Bemeier/bmcv/tests/test_instance.c

// One module per BmcvInstance, with nothing shared behind its back.
//
// The firmware only ever has one module, so a global clock and a file-static
// error latch were harmless there. A simulator or a VCV Rack patch can hold
// several, and two of them sharing a tempo is the kind of bug that is very
// hard to see and impossible to work around. These tests are what keep that
// state out of file scope.

#include "clock_sync.h"
#include "error.h"
#include "hw_setup.h"
#include "instance.h"
#include "presets.h"
#include "testkit.h"
#include "ui_input.h"
#include <string.h>

// A preset backend per instance, so "stored config" is not shared either.
typedef struct
{
  EngineConfig slots[FRAM_CONFIG_SLOTS];
  uint8_t occupied[FRAM_CONFIG_SLOTS];
  int stores;
  int loads;
  int clears;
} FakeFram;

static int8_t fake_store(void* user, const EngineConfig* cfg, int8_t slot)
{
  FakeFram* f = (FakeFram*) user;
  if (slot < 0 || slot >= FRAM_CONFIG_SLOTS)
    return 0;
  f->slots[slot]    = *cfg;
  f->occupied[slot] = 1;
  f->stores++;
  return 1;
}

static int8_t fake_clear(void* user)
{
  FakeFram* f = (FakeFram*) user;
  memset(f->occupied, 0, sizeof(f->occupied));
  f->clears++;
  return 1;
}

static int8_t fake_load(void* user, EngineConfig* cfg, int8_t slot)
{
  FakeFram* f = (FakeFram*) user;
  if (slot < 0 || slot >= FRAM_CONFIG_SLOTS || !f->occupied[slot])
    return 0;
  *cfg = f->slots[slot];
  f->loads++;
  return 1;
}

static void tick(BmcvInstance* m, const InputSample* s, uint32_t now_us) { bmcv_instance_tick(m, s, now_us); }

TEST_CASE(a_fresh_instance_comes_up_with_first_boot_defaults)
{
  BmcvInstance m;
  bmcv_instance_init(&m, NULL, 0);

  // No PresetIo means nothing was stored, which is the first-boot path.
  CHECK(m.engine_config.input_mode[0] == INPUT_CLOCK);
  CHECK(m.engine_config.input_mode[1] == INPUT_RESET);
  CHECK(m.engine_config.scene_a == 0);
  CHECK(m.engine_config.scene_b == 6);
  CHECK(m.engine_config.quantize_mask == 0b111111111111);

  // A module that has never been used is not in an error state: no stored
  // config is the expected condition, and config_validate has already made the
  // defaults safe to index.
  CHECK(!error_any(&m.engine_state));

  // And the UxState is fully wired, so a tick is safe immediately.
  CHECK(m.ux.hw_setup == m.hw_setup);
  CHECK(m.ux.ux_setup == m.ux_setup);
  CHECK(m.ux.engine_config == &m.engine_config);
  CHECK(m.ux.engine_state == &m.engine_state);
  CHECK(m.ux.ui == &m.ui_state);
  CHECK(m.ux.hw_state != NULL);
  CHECK(m.ui_state.momentary_scene == -1);

  InputSample s;
  memset(&s, 0, sizeof(s));
  s.slider_raw = SLIDER_MIN_VALUE;
  tick(&m, &s, MS(1));
}

TEST_CASE(a_stored_config_is_loaded_instead_of_the_defaults)
{
  FakeFram fram;
  memset(&fram, 0, sizeof(fram));

  EngineConfig saved;
  memset(&saved, 0, sizeof(saved));
  saved.scene_a       = 2;
  saved.scene_b       = 3;
  saved.quantize_mask = 0b101010101010;
  for (uint8_t c = 0; c < N_ENCODERS; c++)
  {
    saved.channel_state[c].src_input = -1;
    saved.channel_state[c].src_trig  = -1;
  }
  fram.slots[FRAM_CONFIG_SLOTS - 1]    = saved;
  fram.occupied[FRAM_CONFIG_SLOTS - 1] = 1;

  PresetIo io = {.store = fake_store, .load = fake_load, .user = &fram};

  BmcvInstance m;
  bmcv_instance_init(&m, &io, 0);

  CHECK(fram.loads == 1);
  CHECK(m.engine_config.scene_a == 2);
  CHECK(m.engine_config.scene_b == 3);
  CHECK(!error_any(&m.engine_state)); // nothing went wrong, so no error shown
}

// A module comes back on the parameter page it was left on. This is what the
// field moved out of UiState for: UiState is the half that is deliberately not
// saved, so while it lived there every power cycle landed on a fixed page.
TEST_CASE(the_selected_parameter_survives_a_power_cycle)
{
  FakeFram fram;
  memset(&fram, 0, sizeof(fram));
  PresetIo io = {.store = fake_store, .load = fake_load, .user = &fram};

  BmcvInstance m;
  bmcv_instance_init(&m, &io, 0);
  CHECK(m.engine_config.selected_param == CH_PARAM_OFS); // nothing stored yet

  // The user picks a page, and the autosave slot takes it.
  m.engine_config.selected_param = CH_PARAM_PHS;
  CHECK(ux_preset_store(&m.ux, CONFIG_AUTOSAVE_SLOT) == 1);

  // Power cycle: a brand new instance over the same storage.
  BmcvInstance again;
  bmcv_instance_init(&again, &io, 0);
  CHECK(again.engine_config.selected_param == CH_PARAM_PHS);
}

// ...and with nothing stored at all it is OFS, not whatever a zeroed byte
// would have made it.
TEST_CASE(a_first_boot_selects_the_offset_parameter)
{
  BmcvInstance m;
  bmcv_instance_init(&m, NULL, 0);
  CHECK(m.engine_config.selected_param == CH_PARAM_OFS);
}

// The point of the whole exercise.
TEST_CASE(two_instances_run_independent_clocks)
{
  BmcvInstance a, b;
  bmcv_instance_init(&a, NULL, 0);
  bmcv_instance_init(&b, NULL, 0);

  InputSample sa, sb;
  memset(&sa, 0, sizeof(sa));
  memset(&sb, 0, sizeof(sb));
  sa.slider_raw = SLIDER_MIN_VALUE;
  sb.slider_raw = SLIDER_MIN_VALUE;

  // Both boot with input 0 as INPUT_CLOCK. Feed a at 2Hz and b at 1Hz.
  uint8_t clock_ch = a.hw_setup->input_adc_idx[0];

  uint32_t t = 0;
  for (int i = 0; i < 40; i++)
  {
    t += MS(125);

    sa.cv_trig[clock_ch] = 1;
    tick(&a, &sa, t);
    sa.cv_trig[clock_ch] = 0;

    if (i % 2 == 1) // half as often
    {
      sb.cv_trig[clock_ch] = 1;
      tick(&b, &sb, t);
      sb.cv_trig[clock_ch] = 0;
    }
    else
    {
      tick(&b, &sb, t);
    }
  }

  CHECK_NEAR(a.engine_state.clock.beat_freq_smooth, 2.0, 0.05);
  CHECK_NEAR(b.engine_state.clock.beat_freq_smooth, 1.0, 0.05);
  CHECK(a.engine_state.clock.beat_counter != b.engine_state.clock.beat_counter);
}

TEST_CASE(two_instances_do_not_share_error_flags)
{
  BmcvInstance a, b;
  bmcv_instance_init(&a, NULL, 0);
  bmcv_instance_init(&b, NULL, 0);

  CHECK(!error_any(&a.engine_state));
  CHECK(!error_any(&b.engine_state));

  error_set(&a.engine_state, 3);
  CHECK(error_get(&a.engine_state, 3));
  CHECK(!error_get(&b.engine_state, 3));
  CHECK(!error_any(&b.engine_state));

  error_clear(&a.engine_state);
  error_set(&b.engine_state, 5);
  CHECK(!error_any(&a.engine_state));
  CHECK(error_get(&b.engine_state, 5));
}

TEST_CASE(two_instances_do_not_share_input_or_ui_state)
{
  BmcvInstance a, b;
  bmcv_instance_init(&a, NULL, 0);
  bmcv_instance_init(&b, NULL, 0);

  InputSample sa, sb;
  memset(&sa, 0, sizeof(sa));
  memset(&sb, 0, sizeof(sb));
  sa.slider_raw = 4000;
  sb.slider_raw = 6000;

  int8_t btn          = a.ux_setup->ctrl_buttons[SHIFT_STATE_QNT].button;
  sa.button_down[btn] = 1;
  sa.encoder_pos[0]   = 17;

  // Long enough for the QNT hold to cross UI_T_HOLD and latch the mode.
  // Against the constant, not a number that happened to clear it once.
  for (uint32_t i = 1; i <= UI_T_HOLD / MS(1) + 50; i++)
  {
    tick(&a, &sa, MS(i));
    tick(&b, &sb, MS(i));
  }

  CHECK(a.ux.hw_state->slider_state == 4000);
  CHECK(b.ux.hw_state->slider_state == 6000);
  CHECK(a.ux.hw_state->button_state[btn] == 1);
  CHECK(b.ux.hw_state->button_state[btn] == 0);
  CHECK(a.ux.hw_state->encoder_state[0] == 17);
  CHECK(b.ux.hw_state->encoder_state[0] == 0);

  // Holding QNT put a into that mode; b must be untouched.
  CHECK(a.ui_state.shift_state == SHIFT_STATE_QNT);
  CHECK(b.ui_state.shift_state == SHIFT_STATE_NONE);
}

TEST_CASE(two_instances_do_not_share_preset_storage)
{
  FakeFram fa, fb;
  memset(&fa, 0, sizeof(fa));
  memset(&fb, 0, sizeof(fb));
  PresetIo ioa = {.store = fake_store, .load = fake_load, .user = &fa};
  PresetIo iob = {.store = fake_store, .load = fake_load, .user = &fb};

  BmcvInstance a, b;
  bmcv_instance_init(&a, &ioa, 0);
  bmcv_instance_init(&b, &iob, 0);

  a.engine_config.scene_b = 1;
  CHECK(ux_preset_store(&a.ux, 0) == 1);

  CHECK(fa.stores == 1);
  CHECK(fb.stores == 0);
  CHECK(fa.occupied[0]);
  CHECK(!fb.occupied[0]);
}

// Each instance renders into its own framebuffer.
TEST_CASE(two_instances_do_not_share_the_led_framebuffer)
{
  BmcvInstance a, b;
  bmcv_instance_init(&a, NULL, 0);
  bmcv_instance_init(&b, NULL, 0);

  InputSample sa, sb;
  memset(&sa, 0, sizeof(sa));
  memset(&sb, 0, sizeof(sb));
  sa.slider_raw = SLIDER_MIN_VALUE;
  sb.slider_raw = SLIDER_MIN_VALUE;

  sa.button_down[a.ux_setup->ctrl_buttons[SHIFT_STATE_QNT].button] = 1;

  for (uint32_t i = 1; i <= UI_T_HOLD / MS(1) + 50; i++)
  {
    tick(&a, &sa, MS(i));
    tick(&b, &sb, MS(i));
  }

  int8_t qnt_led = a.ux_setup->ctrl_buttons[SHIFT_STATE_QNT].led;
  CHECK(qnt_led >= 0);

  // a is in QNT and b is not, so their framebuffers must differ somewhere.
  uint8_t differs = 0;
  for (uint8_t i = 0; i < LED_COUNT; i++)
  {
    const LedRgb* la = &a.engine_state.leds[i];
    const LedRgb* lb = &b.engine_state.leds[i];
    if (la->r != lb->r || la->g != lb->g || la->b != lb->b)
      differs = 1;
  }
  CHECK(differs);
}

/* ---- commands from outside the module ------------------------------------ */

// The whole risk of a command is being performed twice. Both transports rewrite
// their mailboxes continuously, so "act on a change of seq" is what stands
// between one reset and a module that resets for ever.
TEST_CASE(a_command_is_acted_on_once)
{
  FakeFram fram = {0};
  PresetIo io   = {.store = fake_store, .load = fake_load, .clear = fake_clear, .user = &fram};

  BmcvInstance m;
  bmcv_instance_init(&m, &io, 0);

  // Move the module off its power-on state so a reset is visible.
  m.engine_config.selected_param = 3;
  m.ui_state.shift_state         = 2;

  m.command.op  = REMOTE_OP_RESET;
  m.command.seq = 1;

  CHECK(bmcv_instance_take_command(&m, &io, 1000) == 1);
  CHECK(m.ui_state.shift_state == SHIFT_STATE_NONE);

  // Same sequence number, so nothing happens however often it is seen.
  m.ui_state.shift_state = 2;
  for (int i = 0; i < 5; i++)
  {
    CHECK(bmcv_instance_take_command(&m, &io, 2000) == 0);
  }
  CHECK(m.ui_state.shift_state == 2);

  // A new one is acted on again.
  m.command.seq = 2;
  CHECK(bmcv_instance_take_command(&m, &io, 3000) == 1);
  CHECK(m.ui_state.shift_state == SHIFT_STATE_NONE);
}

// A fresh module holds seq 0 and has been asked nothing, so nothing may happen
// before a host ever speaks - a reset on the first pass would be a module that
// wipes itself at power-on.
TEST_CASE(a_silent_mailbox_asks_for_nothing)
{
  BmcvInstance m;
  bmcv_instance_init(&m, NULL, 0);

  m.engine_config.selected_param = 3;
  CHECK(bmcv_instance_take_command(&m, NULL, 1000) == 0);
  CHECK(m.engine_config.selected_param == 3);
}

TEST_CASE(a_wipe_forgets_storage_before_reloading_it)
{
  FakeFram fram = {0};
  PresetIo io   = {.store = fake_store, .load = fake_load, .clear = fake_clear, .user = &fram};

  BmcvInstance m;
  bmcv_instance_init(&m, &io, 0);

  // Something in the autosave slot, so a plain reset would come back to it.
  m.engine_config.selected_param = 3;
  ux_preset_store(&m.ux, CONFIG_AUTOSAVE_SLOT);
  CHECK(fram.occupied[CONFIG_AUTOSAVE_SLOT] == 1);

  m.command.op  = REMOTE_OP_RESET;
  m.command.seq = 1;
  bmcv_instance_take_command(&m, &io, 1000);
  CHECK(m.engine_config.selected_param == 3); // reloaded what was stored

  m.command.op  = REMOTE_OP_RESET_WIPE;
  m.command.seq = 2;
  bmcv_instance_take_command(&m, &io, 2000);

  CHECK(fram.clears == 1);
  CHECK(fram.occupied[CONFIG_AUTOSAVE_SLOT] == 0);
  // Nothing left to load, so the module is on its first-boot defaults.
  CHECK(m.engine_config.selected_param != 3);
}

// Storage that cannot be wiped is legal - a host may simply not offer it - and
// must not turn the reset half of the command into a crash.
TEST_CASE(a_wipe_without_a_clear_still_resets)
{
  FakeFram fram = {0};
  PresetIo io   = {.store = fake_store, .load = fake_load, .clear = NULL, .user = &fram};

  BmcvInstance m;
  bmcv_instance_init(&m, &io, 0);
  m.ui_state.shift_state = 2;

  m.command.op  = REMOTE_OP_RESET_WIPE;
  m.command.seq = 1;
  CHECK(bmcv_instance_take_command(&m, &io, 1000) == 1);
  CHECK(m.ui_state.shift_state == SHIFT_STATE_NONE);
}

int main(void)
{
  RUN_TEST(a_fresh_instance_comes_up_with_first_boot_defaults);
  RUN_TEST(a_stored_config_is_loaded_instead_of_the_defaults);
  RUN_TEST(the_selected_parameter_survives_a_power_cycle);
  RUN_TEST(a_first_boot_selects_the_offset_parameter);
  RUN_TEST(two_instances_run_independent_clocks);
  RUN_TEST(two_instances_do_not_share_error_flags);
  RUN_TEST(two_instances_do_not_share_input_or_ui_state);
  RUN_TEST(two_instances_do_not_share_preset_storage);
  RUN_TEST(two_instances_do_not_share_the_led_framebuffer);
  RUN_TEST(a_command_is_acted_on_once);
  RUN_TEST(a_silent_mailbox_asks_for_nothing);
  RUN_TEST(a_wipe_forgets_storage_before_reloading_it);
  RUN_TEST(a_wipe_without_a_clear_still_resets);
  return TESTKIT_SUMMARY();
}
