Bemeier/bmcv/tools/wavetables.h

#pragma once

#define N 256
#define M 99

const int16_t shape_table[M][N] = {
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
